xhusar2/night_vision_devices-nvg_monocular/hardware/wiring/nvg_monocular.kicad_sch

## KiCad design hardware/wiring/nvg_monocular.kicad_sch (2026-02-18)

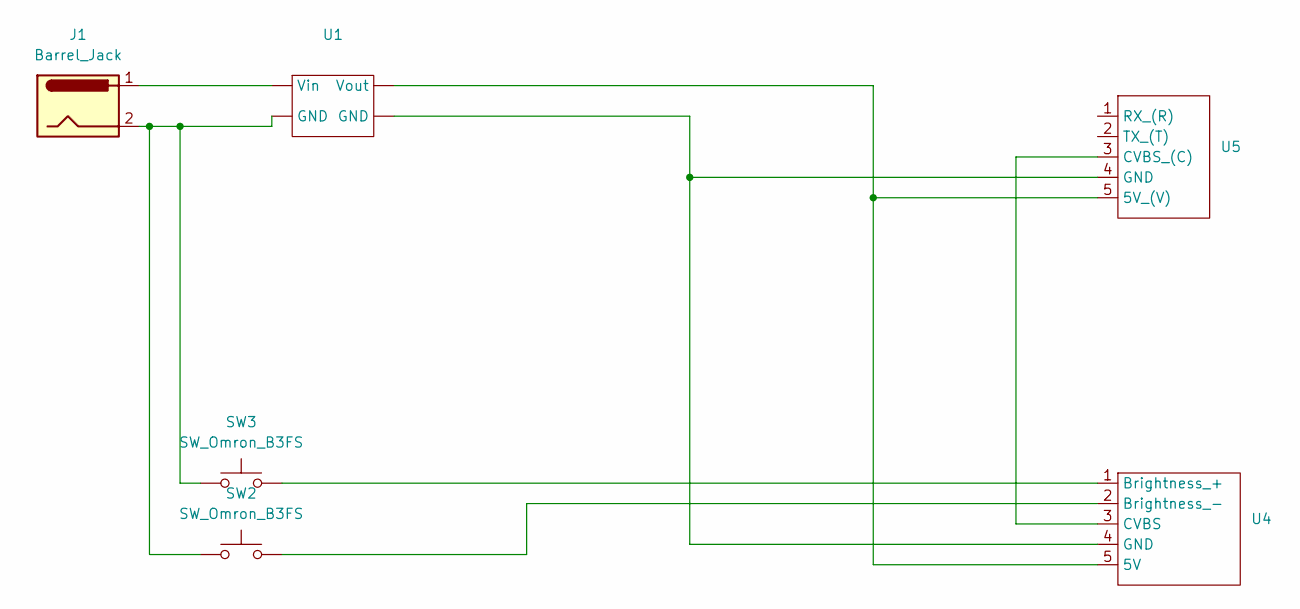
[picture p6: schematic nvg_monocular.kicad_sch]

Parts:
J1: Barrel_Jack
SW2, SW3: SW_Omron_B3FS
U1, U4, U5: (no value)

Connections:
unnamed: J1.1, U1.
unnamed: J1.2, SW2.1, SW3.1, U1.
unnamed: SW2.2, U4.2 (Brightness_-)
unnamed: SW3.2, U4.1 (Brightness_+)
unnamed: U1., U4.4 (GND), U4.5 (5V), U5.4 (GND), U5.5 (5V_(V))
unnamed: U4.3 (CVBS), U5.3 (CVBS_(C))
